zacrussgamer11-boop/robotics-arm-project/project_info/V1 Complete/PHOTOS/IMG_8290.jpg

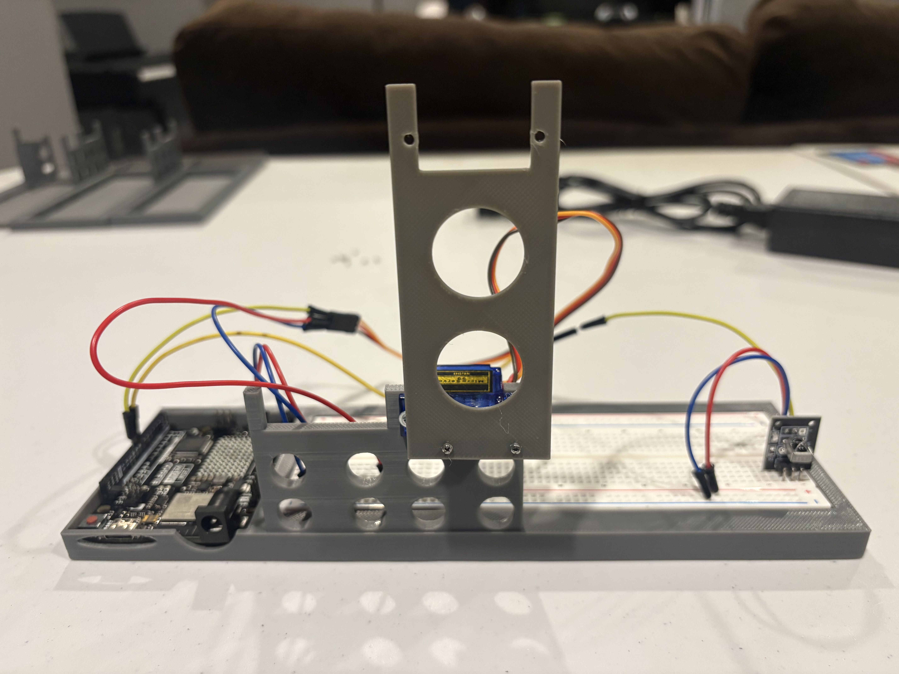
project_info/V1 Complete/PHOTOS/IMG_8290.jpg
